Axialis/one-wire-reader/FW/Core/Inc/macro.h

/*
 * macro.h
 *
 *  Created on: 16 сент. 2021 г.
 *      Author: Alexandr
 */

#ifndef INC_MACRO_H_
#define INC_MACRO_H_

void REL_1(int x);
void REL_2(int x);
void REL_3(int x);
void REL_4(int x);
void REL_5(int x);
void REL_6(int x);
void REL_7(int x);
void REL_8(int x);


#endif /* INC_MACRO_H_ */
