Axialis/one-wire-reader/FW/Core/Src/macro.c

/*
 * macro.c
 *
 *  Created on: 16 сент. 2021 г.
 *      Author: Alexandr
 */

#include "macro.h"
#include "gpio.h"

void REL_1(int x)
{
	if(x == 1)
	HAL_GPIO_WritePin(GPIOE, GPIO_PIN_8, GPIO_PIN_SET);
	if(x == 0)
	HAL_GPIO_WritePin(GPIOE, GPIO_PIN_8, GPIO_PIN_RESET);
}

void REL_2(int x)
{
	if(x == 1)
	HAL_GPIO_WritePin(GPIOE, GPIO_PIN_9, GPIO_PIN_SET);
	if(x == 0)
	HAL_GPIO_WritePin(GPIOE, GPIO_PIN_9, GPIO_PIN_RESET);
}

void REL_3(int x)
{
	if(x == 1)
	HAL_GPIO_WritePin(GPIOE, GPIO_PIN_10, GPIO_PIN_SET);
	if(x == 0)
	HAL_GPIO_WritePin(GPIOE, GPIO_PIN_10, GPIO_PIN_RESET);
}

void REL_4(int x)
{
	if(x == 1)
	HAL_GPIO_WritePin(GPIOE, GPIO_PIN_11, GPIO_PIN_SET);
	if(x == 0)
	HAL_GPIO_WritePin(GPIOE, GPIO_PIN_11, GPIO_PIN_RESET);
}

void REL_5(int x)
{
	if(x == 1)
	HAL_GPIO_WritePin(GPIOE, GPIO_PIN_12, GPIO_PIN_SET);
	if(x == 0)
	HAL_GPIO_WritePin(GPIOE, GPIO_PIN_12, GPIO_PIN_RESET);
}

void REL_6(int x)
{
	if(x == 1)
	HAL_GPIO_WritePin(GPIOE, GPIO_PIN_13, GPIO_PIN_SET);
	if(x == 0)
	HAL_GPIO_WritePin(GPIOE, GPIO_PIN_13, GPIO_PIN_RESET);
}

void REL_7(int x)
{
	if(x == 1)
	HAL_GPIO_WritePin(GPIOE, GPIO_PIN_14, GPIO_PIN_SET);
	if(x == 0)
	HAL_GPIO_WritePin(GPIOE, GPIO_PIN_14, GPIO_PIN_RESET);
}

void REL_8(int x)
{
	if(x == 1)
	HAL_GPIO_WritePin(GPIOE, GPIO_PIN_15, GPIO_PIN_SET);
	if(x == 0)
	HAL_GPIO_WritePin(GPIOE, GPIO_PIN_15, GPIO_PIN_RESET);
}
